wjhrdy/point-and-shoot-adapter/lenses/nikon-fun_touch_6-28mm-f5.6.scad

knurl_height = 5.43;             // mm, height of knurled ring.
lens_hole_diam = 15.85;          // mm, lens hole inner diameter (configurable)
lens_cyl_depth = 3.57;           // mm, depth of lens holding cylinder
lens_offset = -5;             // mm, positive = lens protrudes in front of knurled face, zero/negative = flush or recessed
l39_thread_length = 4.32; // mm, total thread length
